thomp901/PyroNet/firmware/wisun_soc_cli/autogen/sl_component_catalog.h

#ifndef SL_COMPONENT_CATALOG_H
#define SL_COMPONENT_CATALOG_H

// APIs present in project
#define SL_CATALOG_CLI_PRESENT
#define SL_CATALOG_CLOCK_MANAGER_PRESENT
#define SL_CATALOG_CMSIS_OS_COMMON_PRESENT
#define SL_CATALOG_DEVICE_INIT_CORE_PRESENT
#define SL_CATALOG_EMLIB_CORE_PRESENT
#define SL_CATALOG_GPIO_PRESENT
#define SL_CATALOG_INTERRUPT_MANAGER_PRESENT
#define SL_CATALOG_IOSTREAM_PRESENT
#define SL_CATALOG_IOSTREAM_EUSART_PRESENT
#define SL_CATALOG_RETARGET_STDIO_PRESENT
#define SL_CATALOG_IOSTREAM_UART_COMMON_PRESENT
#define SL_CATALOG_MEMORY_MANAGER_PRESENT
#define SL_CATALOG_KERNEL_PRESENT
#define SL_CATALOG_MICRIUMOS_KERNEL_PRESENT
#define SL_CATALOG_NVM3_DEFAULT_PRESENT
#define SL_CATALOG_NVM3_PRESENT
#define SL_CATALOG_PSA_CRYPTO_PRESENT
#define SL_CATALOG_RAIL_LIB_PRESENT
#define SL_CATALOG_RAIL_UTIL_PTI_PRESENT
#define SL_CATALOG_RAIL_UTIL_RF_PATH_SWITCH_PRESENT
#define SL_CATALOG_SE_MANAGER_PRESENT
#define SL_CATALOG_SEGGER_RTT_PRESENT
#define SL_CATALOG_SL_CORE_PRESENT
#define SL_CATALOG_SL_MAIN_PRESENT
#define SL_CATALOG_SLEEPTIMER_PRESENT
#define SL_CATALOG_WISUN_CLI_UTIL_PRESENT
#define SL_CATALOG_WISUN_CONFIG_PRESENT
#define SL_CATALOG_WISUN_CONFIGURATION_PRESENT
#define SL_CATALOG_WISUN_CRYPTO_PRESENT
#define SL_CATALOG_WISUN_DEFAULT_PHY_PRESENT
#define SL_CATALOG_WISUN_DEFAULT_RADIOCONF_PRESENT
#define SL_CATALOG_BRD2705A_PRESENT
#define SL_CATALOG_WISUN_RB_DETECTION_PRESENT
#define SL_CATALOG_WISUN_RF_TEST_PRESENT
#define SL_CATALOG_WISUN_STACK_PRESENT
#define SL_CATALOG_WISUN_STACK_DEBUG_PRESENT
#define SL_CATALOG_WISUN_FFN_DEVICE_SUPPORT_PRESENT
#define SL_CATALOG_WISUN_LFN_DEVICE_SUPPORT_PRESENT

#endif // SL_COMPONENT_CATALOG_H
